hykilpikonna/open-keyprec/models/Exports/45-G#5.stl

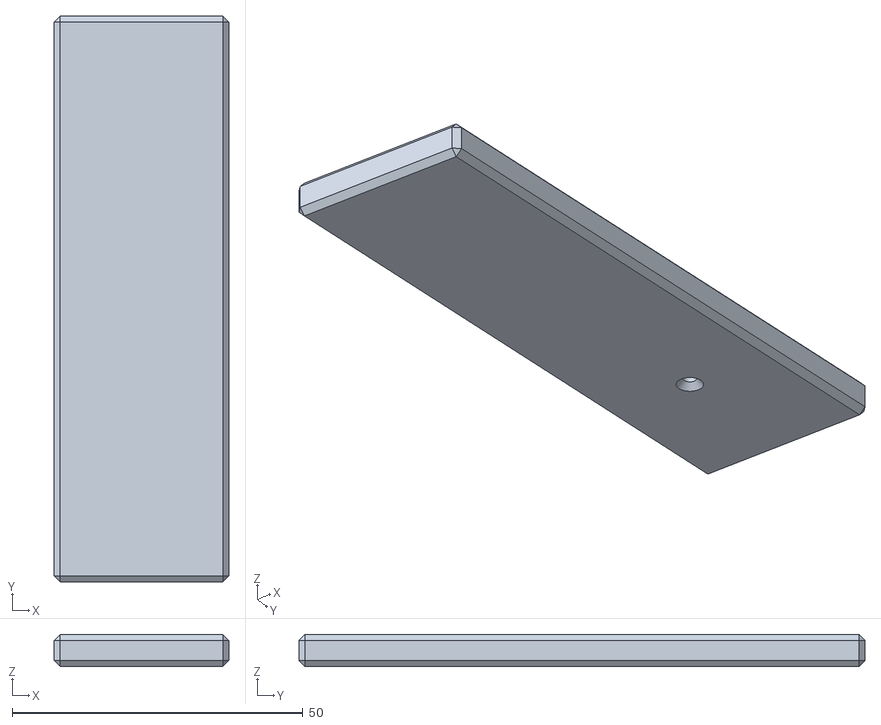
[picture p15: CAD file, 2023-03-16]
models/Exports/45-G#5.stl
30.0 x 97.3 x 5.50
