hykilpikonna/open-keyprec/models/Exports/42-F5.stl

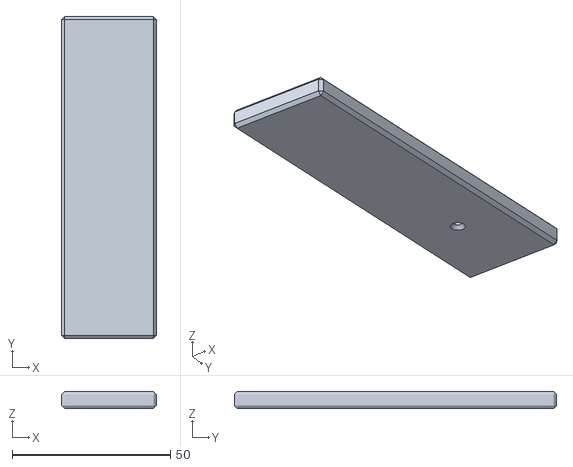
[picture p16: CAD file, 2023-03-16]
models/Exports/42-F5.stl
30.0 x 101.8 x 5.50
