hykilpikonna/open-keyprec/models/Exports/22-A3.stl

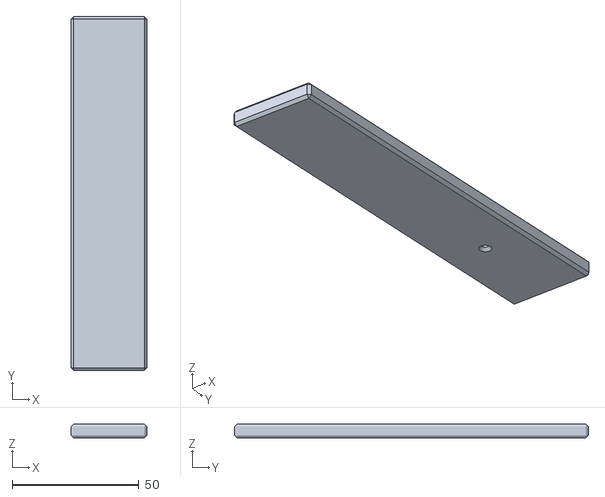
[picture p17: CAD file, 2023-03-16]
models/Exports/22-A3.stl
30.0 x 139.8 x 5.50
