hykilpikonna/open-keyprec/models/Exports/28-D#4.stl

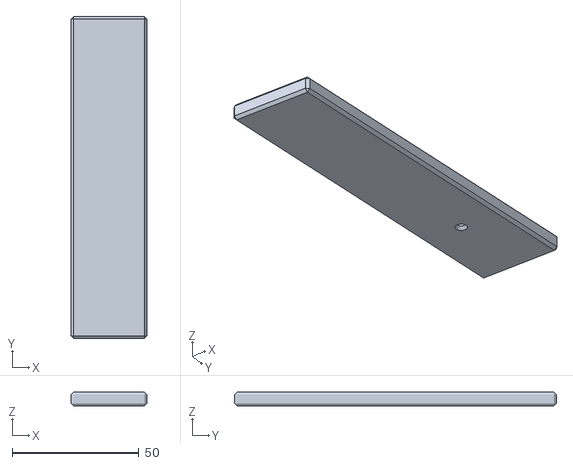
[picture p18: CAD file, 2023-03-16]
models/Exports/28-D#4.stl
30.0 x 127.0 x 5.50
