hykilpikonna/open-keyprec/models/Exports/07-F#2.stl

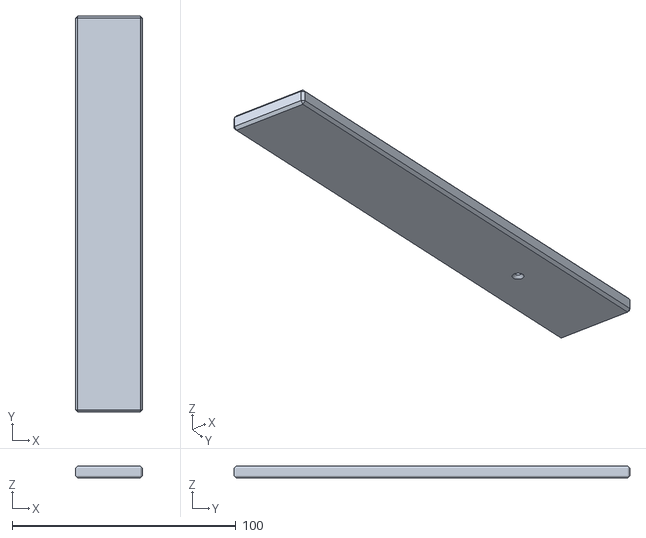
[picture p19: CAD file, 2023-03-16]
models/Exports/07-F#2.stl
30.0 x 177.0 x 5.50
