hykilpikonna/open-keyprec/models/Exports/41-E5.stl

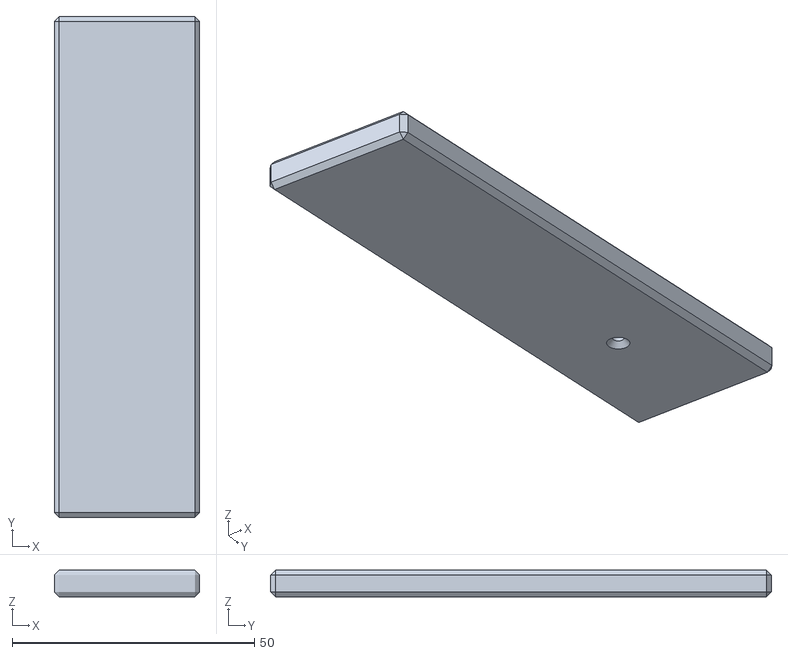
[picture p20: CAD file, 2023-03-16]
models/Exports/41-E5.stl
30.0 x 103.4 x 5.50
