hykilpikonna/open-keyprec/models/Exports/52-D#6.stl

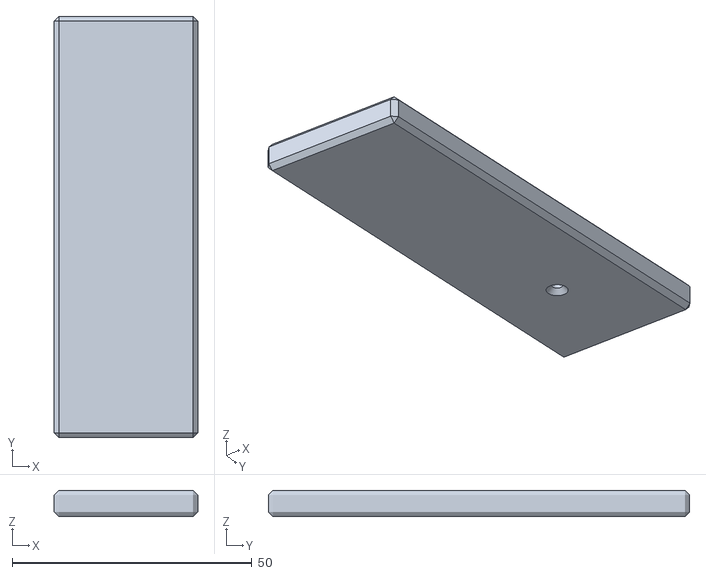
[picture p21: CAD file, 2023-03-16]
models/Exports/52-D#6.stl
30.0 x 87.8 x 5.50
