hykilpikonna/open-keyprec/models/Exports/39-D5.stl

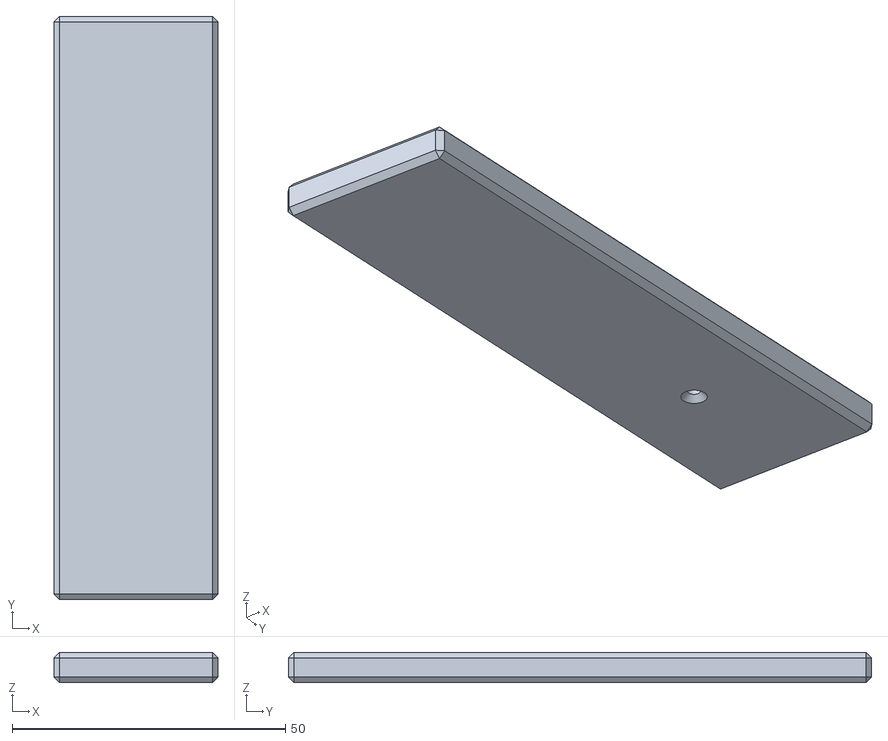
[picture p22: CAD file, 2023-03-16]
models/Exports/39-D5.stl
30.0 x 106.7 x 5.50
