hykilpikonna/open-keyprec/models/Exports/47-A#5.stl

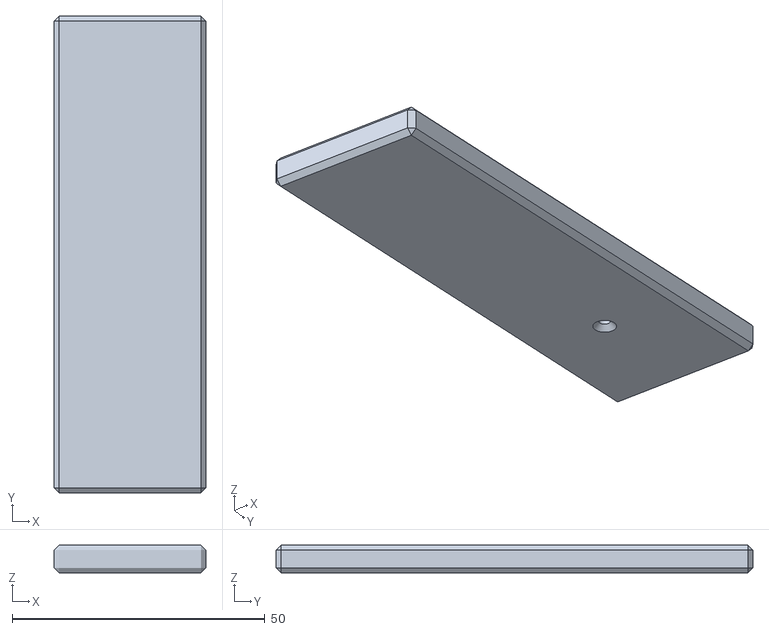
[picture p23: CAD file, 2023-03-16]
models/Exports/47-A#5.stl
30.0 x 94.4 x 5.50
