hykilpikonna/open-keyprec/models/Exports/32-G4.stl

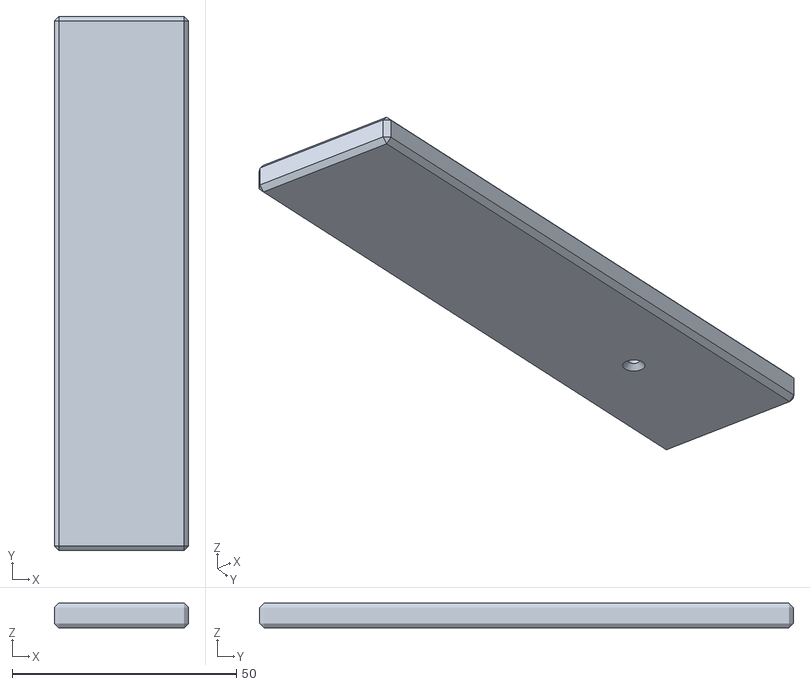
[picture p24: CAD file, 2023-03-16]
models/Exports/32-G4.stl
30.0 x 119.2 x 5.50
