hykilpikonna/open-keyprec/models/Exports/35-A#4.stl

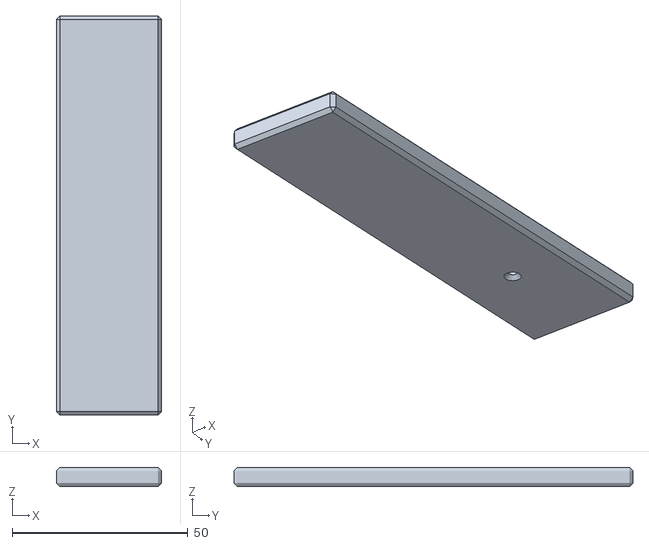
[picture p25: CAD file, 2023-03-16]
models/Exports/35-A#4.stl
30.0 x 113.6 x 5.50
