hykilpikonna/open-keyprec/models/Exports/43-F#5.stl

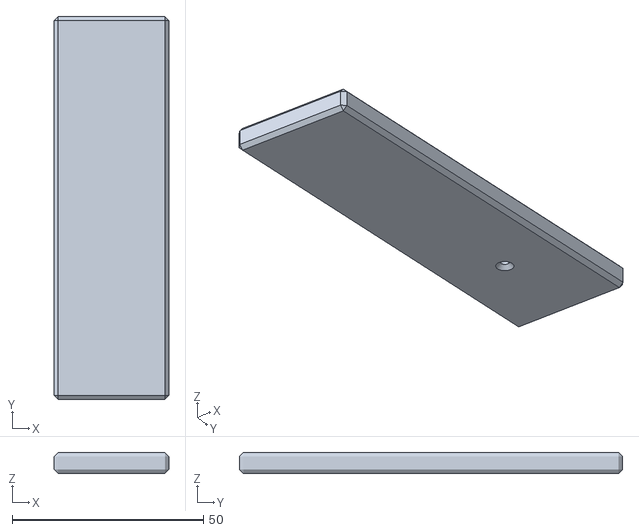
[picture p26: CAD file, 2023-03-16]
models/Exports/43-F#5.stl
30.0 x 100.3 x 5.50
