hykilpikonna/open-keyprec/models/Exports/38-C#5.stl

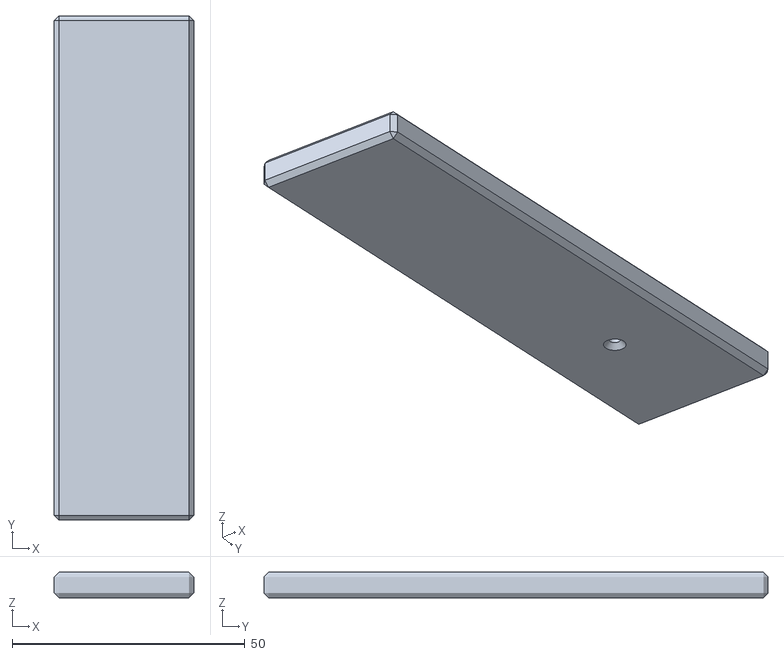
[picture p27: CAD file, 2023-03-16]
models/Exports/38-C#5.stl
30.0 x 108.3 x 5.50
