hykilpikonna/open-keyprec/models/Exports/37-C5.stl

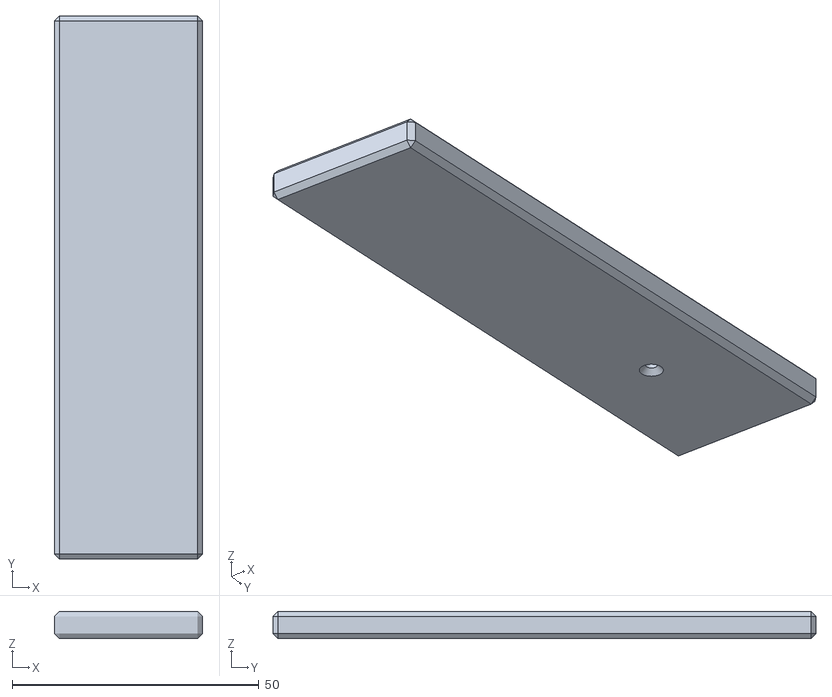
[picture p28: CAD file, 2023-03-16]
models/Exports/37-C5.stl
30.0 x 110.1 x 5.50
