hykilpikonna/open-keyprec/models/Exports/58-A6.stl

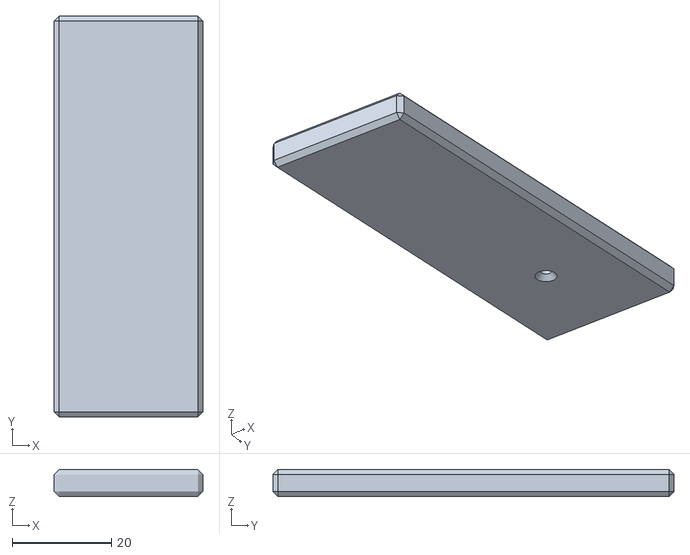
[picture p29: CAD file, 2023-03-16]
models/Exports/58-A6.stl
30.0 x 81.0 x 5.50
