hykilpikonna/open-keyprec/models/Exports/56-G6.stl

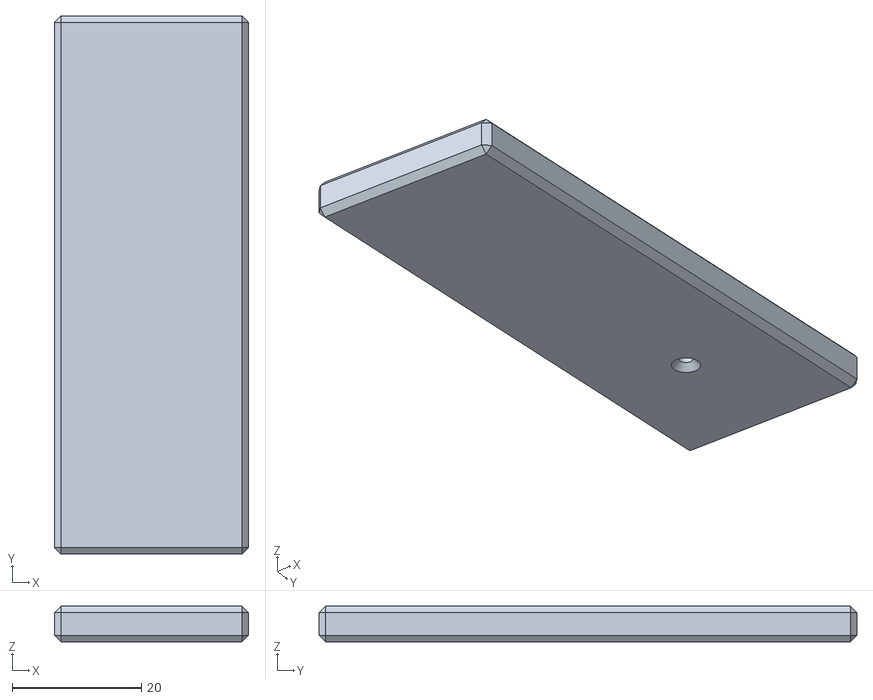
[picture p30: CAD file, 2023-03-16]
models/Exports/56-G6.stl
30.0 x 83.1 x 5.50
