hykilpikonna/open-keyprec/models/Exports/51-D6.stl

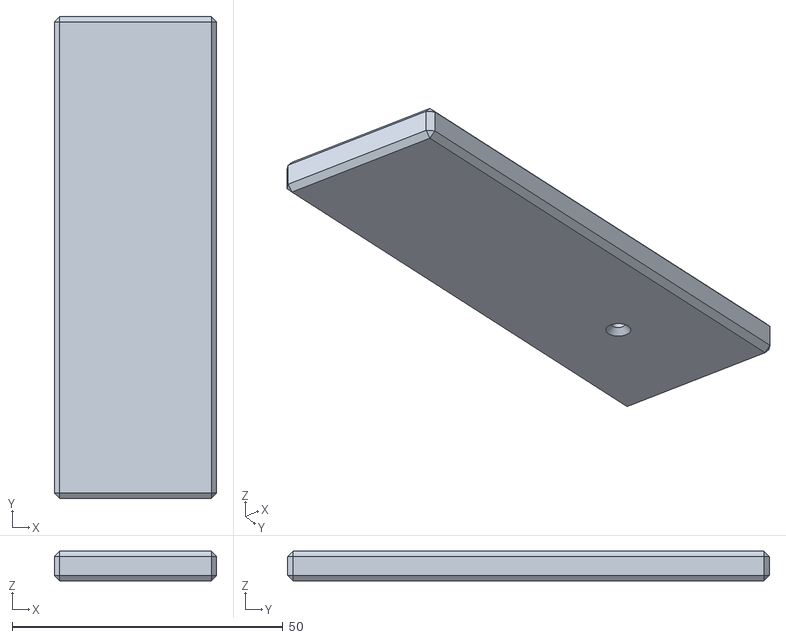
[picture p31: CAD file, 2023-03-16]
models/Exports/51-D6.stl
30.0 x 89.0 x 5.50
