hykilpikonna/open-keyprec/models/Exports/61-C7.stl

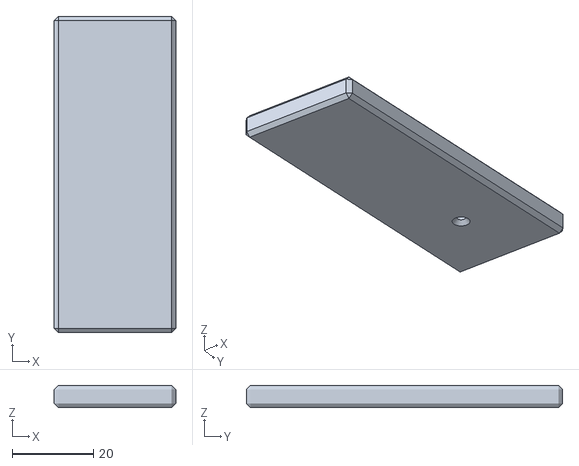
[picture p32: CAD file, 2023-03-16]
models/Exports/61-C7.stl
30.0 x 78.0 x 5.50
