hykilpikonna/open-keyprec/models/Exports/14-C#3.stl

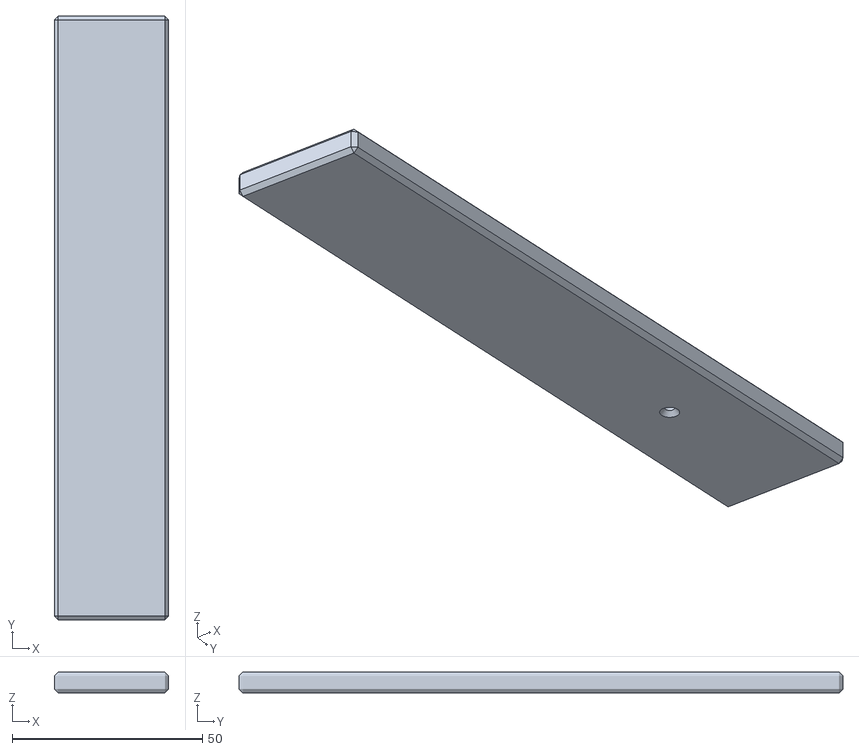
[picture p33: CAD file, 2023-03-16]
models/Exports/14-C#3.stl
30.0 x 158.7 x 5.50
