hykilpikonna/open-keyprec/models/Exports/44-G5.stl

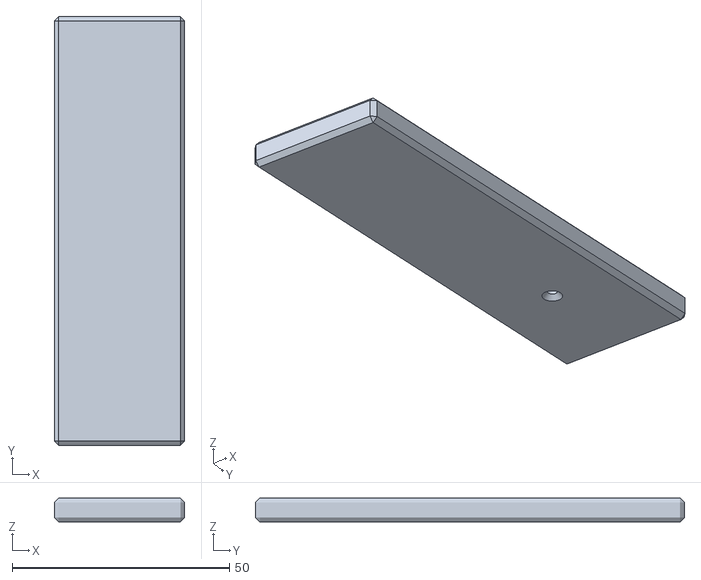
[picture p34: CAD file, 2023-03-16]
models/Exports/44-G5.stl
30.0 x 98.7 x 5.50
