hykilpikonna/open-keyprec/models/Exports/57-G#6.stl

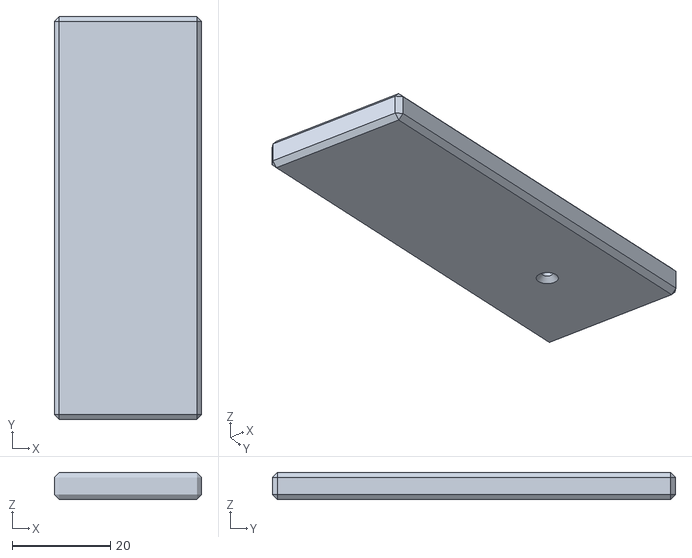
[picture p35: CAD file, 2023-03-16]
models/Exports/57-G#6.stl
30.0 x 82.0 x 5.50
