hykilpikonna/open-keyprec/models/Exports/12-B2.stl

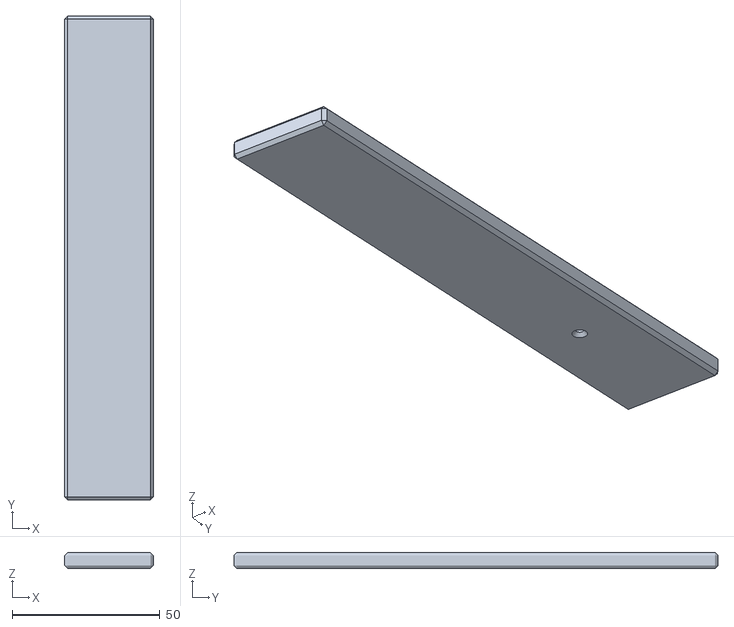
[picture p36: CAD file, 2023-03-16]
models/Exports/12-B2.stl
30.0 x 163.8 x 5.50
