hykilpikonna/open-keyprec/models/Exports/18-F3.stl

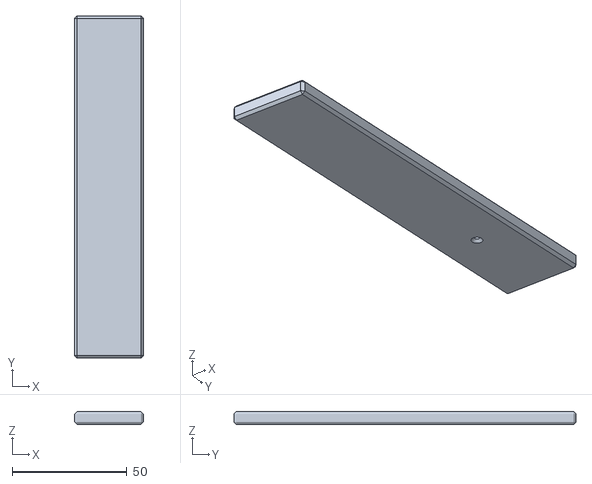
[picture p37: CAD file, 2023-03-16]
models/Exports/18-F3.stl
30.0 x 149.0 x 5.50
