hykilpikonna/open-keyprec/models/Exports/53-E6.stl

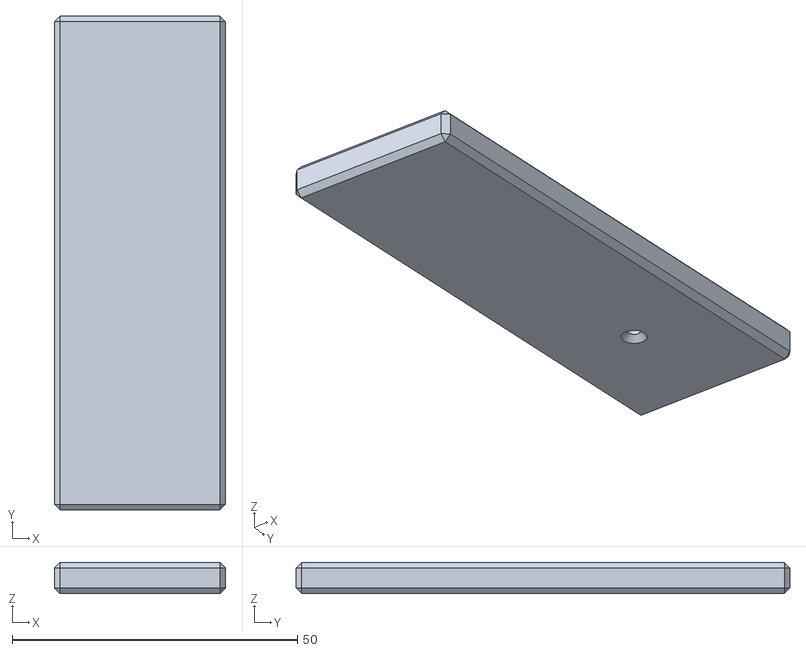
[picture p38: CAD file, 2023-03-16]
models/Exports/53-E6.stl
30.0 x 86.6 x 5.50
