hykilpikonna/open-keyprec/models/Exports/26-C#4.stl

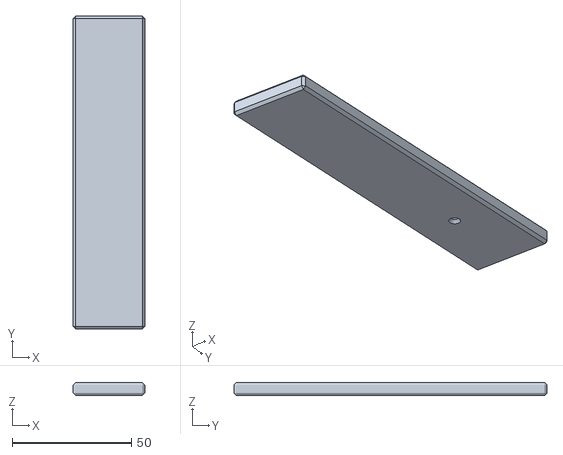
[picture p39: CAD file, 2023-03-16]
models/Exports/26-C#4.stl
30.0 x 131.1 x 5.50
