hykilpikonna/open-keyprec/models/Exports/31-F#4.stl

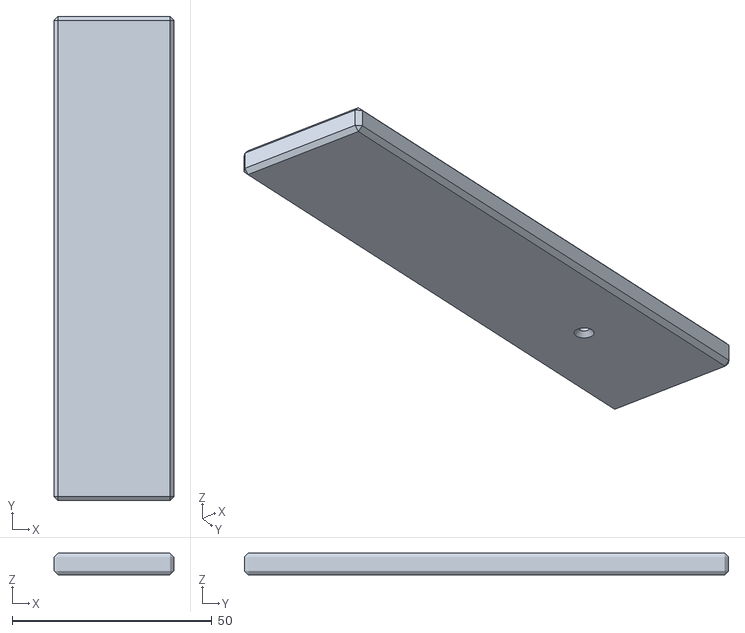
[picture p40: CAD file, 2023-03-16]
models/Exports/31-F#4.stl
30.0 x 121.1 x 5.50
