hykilpikonna/open-keyprec/models/Exports/05-E2.stl

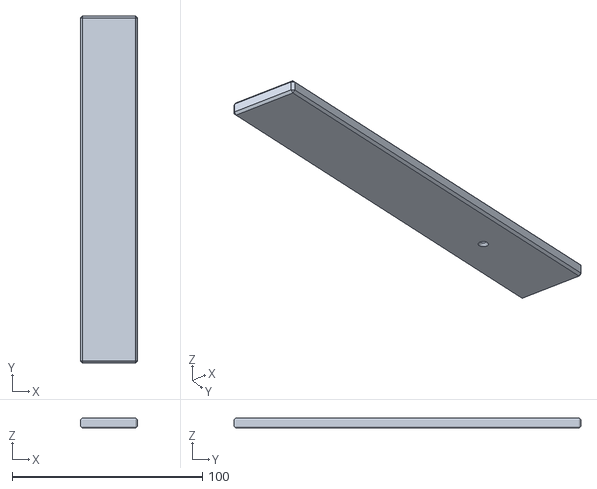
[picture p41: CAD file, 2023-03-16]
models/Exports/05-E2.stl
30.0 x 182.6 x 5.50
