hykilpikonna/open-keyprec/models/Exports/46-A5.stl

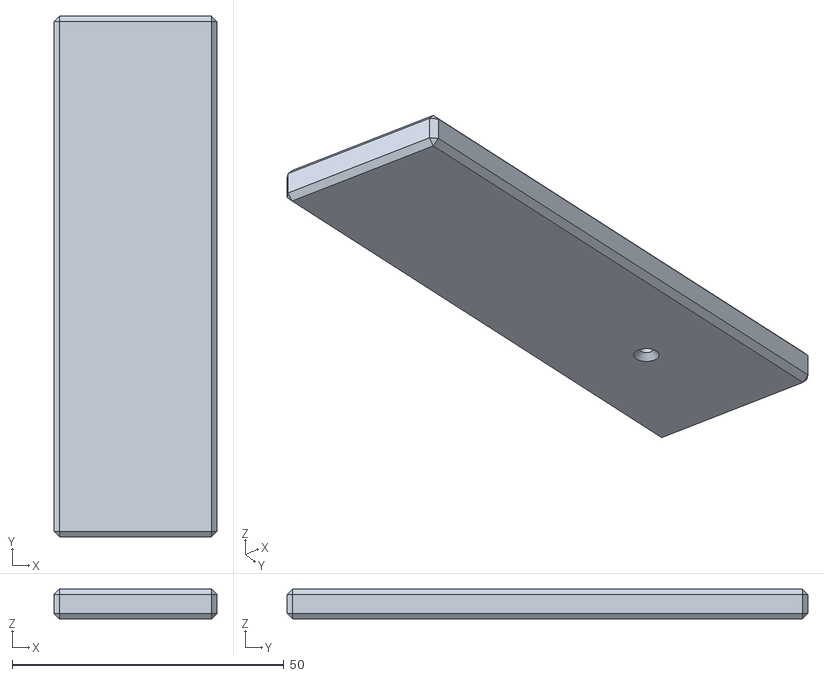
[picture p42: CAD file, 2023-03-16]
models/Exports/46-A5.stl
30.0 x 95.8 x 5.50
