hykilpikonna/open-keyprec/models/Exports/34-A4.stl

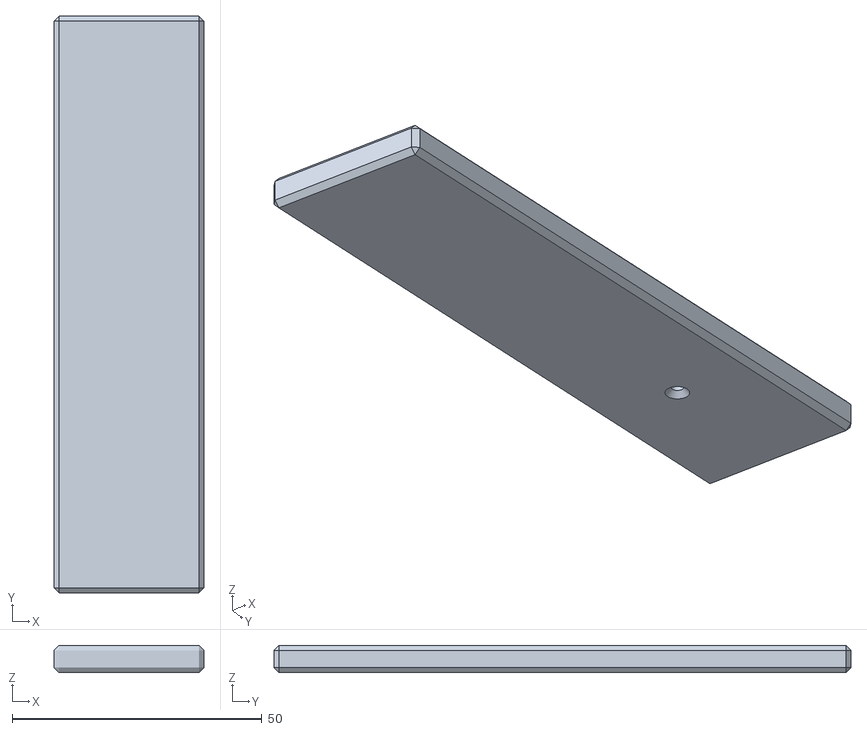
[picture p43: CAD file, 2023-03-16]
models/Exports/34-A4.stl
30.0 x 115.4 x 5.50
