hykilpikonna/open-keyprec/models/Exports/33-G#4.stl

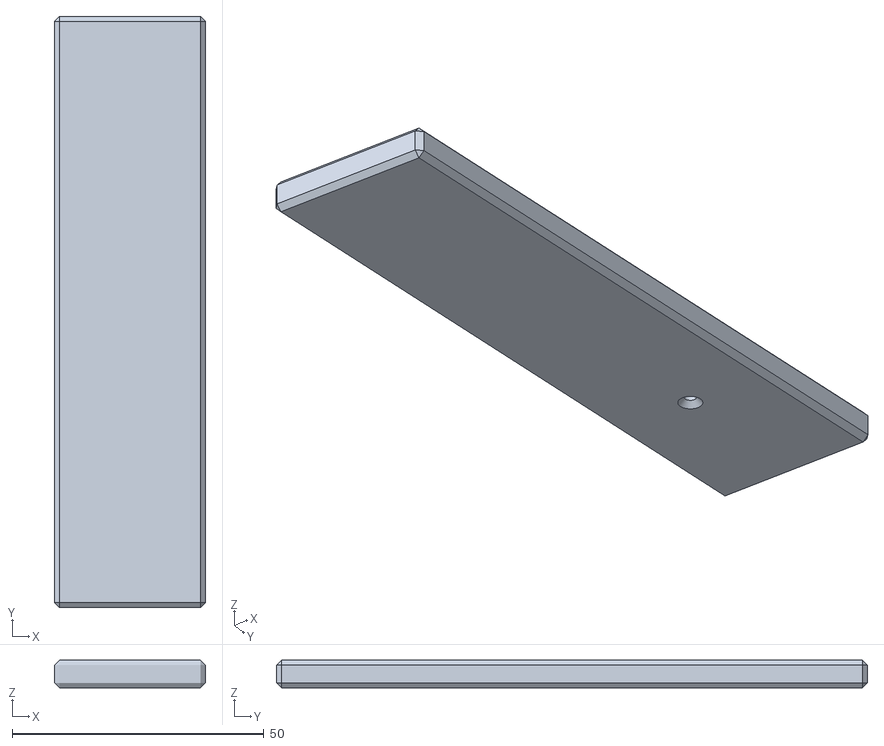
[picture p44: CAD file, 2023-03-16]
models/Exports/33-G#4.stl
30.0 x 117.3 x 5.50
