hykilpikonna/open-keyprec/models/Exports/40-D#5.stl

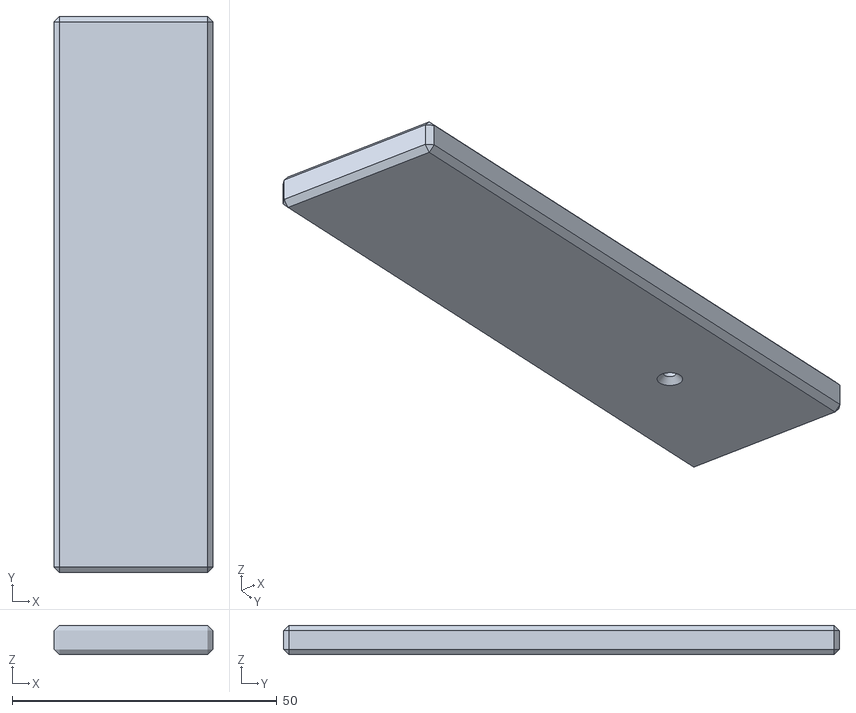
[picture p45: CAD file, 2023-03-16]
models/Exports/40-D#5.stl
30.0 x 105.0 x 5.50
