hykilpikonna/open-keyprec/models/Exports/36-B4.stl

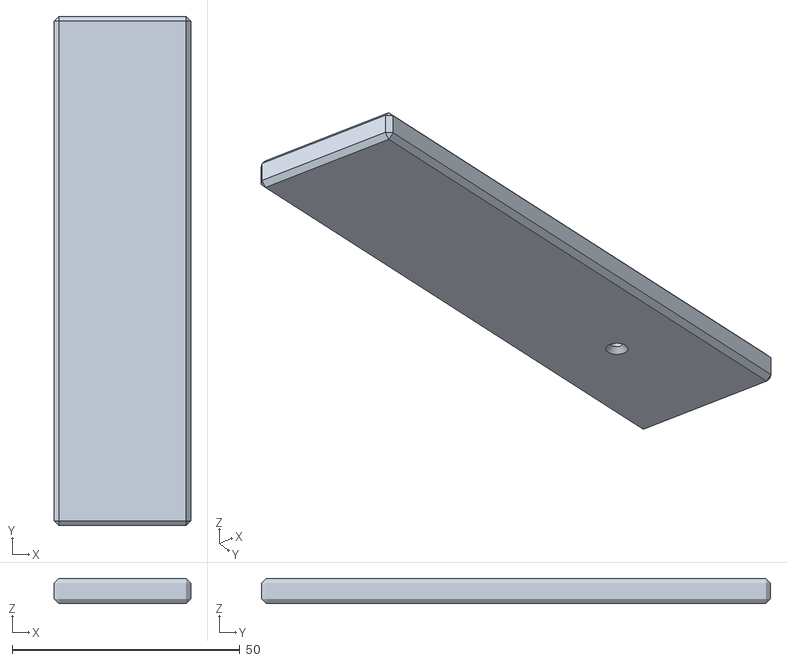
[picture p46: CAD file, 2023-03-16]
models/Exports/36-B4.stl
30.0 x 111.8 x 5.50
