hykilpikonna/open-keyprec/models/Exports/24-B3.stl

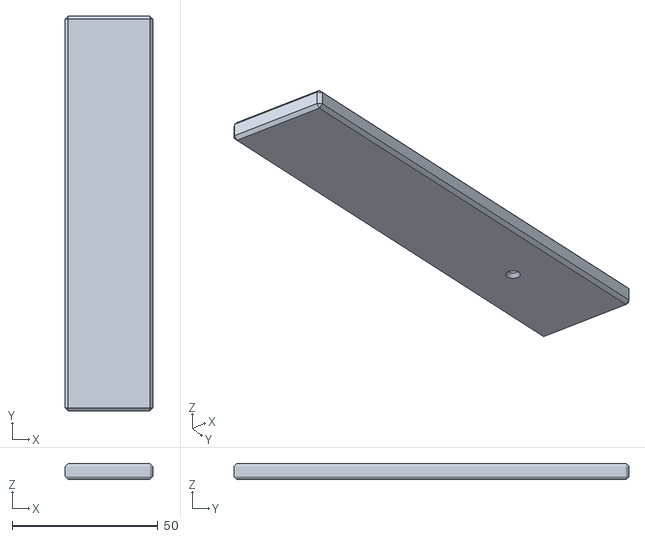
[picture p47: CAD file, 2023-03-16]
models/Exports/24-B3.stl
30.0 x 135.4 x 5.50
