hykilpikonna/open-keyprec/models/Exports/55-F#6.stl

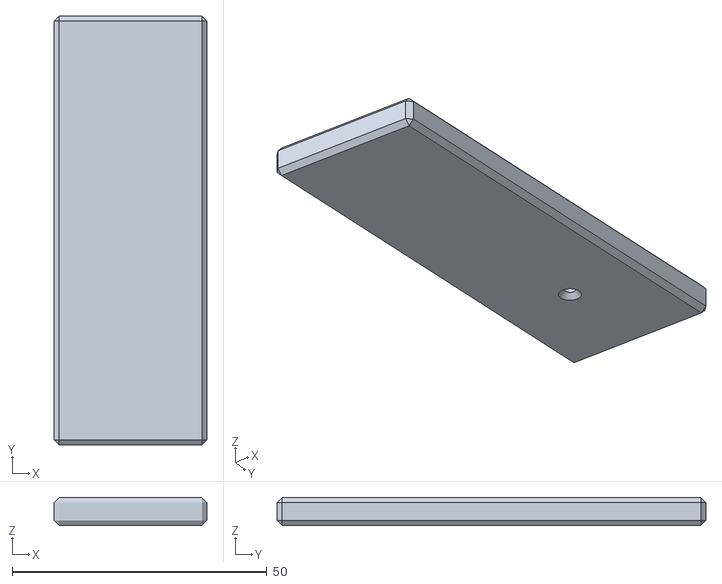
[picture p48: CAD file, 2023-03-16]
models/Exports/55-F#6.stl
30.0 x 84.2 x 5.50
