hykilpikonna/open-keyprec/models/Exports/25-C4.stl

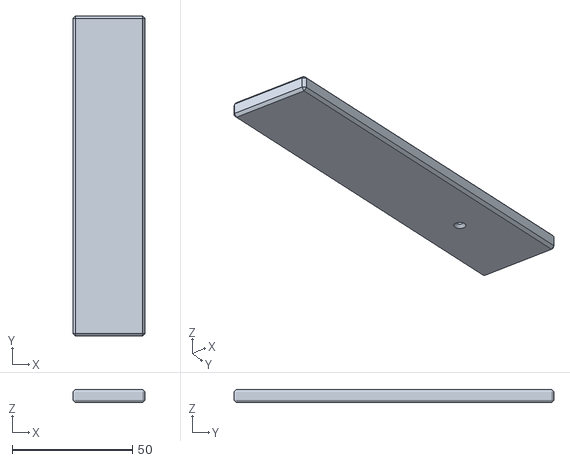
[picture p49: CAD file, 2023-03-16]
models/Exports/25-C4.stl
30.0 x 133.3 x 5.50
