hykilpikonna/open-keyprec/models/Exports/59-A#6.stl

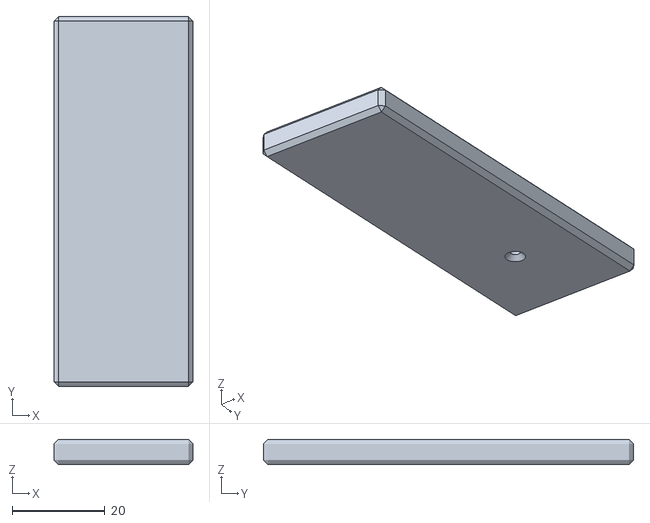
[picture p50: CAD file, 2023-03-16]
models/Exports/59-A#6.stl
30.0 x 79.9 x 5.50
