hykilpikonna/open-keyprec/models/Exports/60-B6.stl

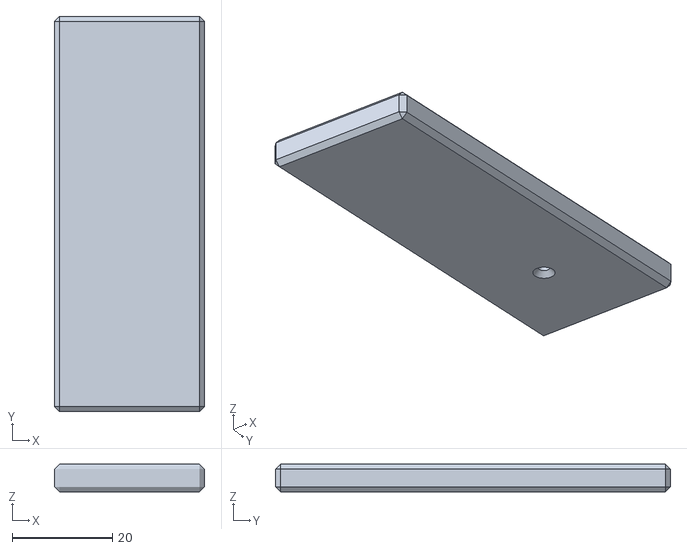
[picture p51: CAD file, 2023-03-16]
models/Exports/60-B6.stl
30.0 x 79.0 x 5.50
